tobigun/EavesDrum/doc/images/1.1/module.jpg

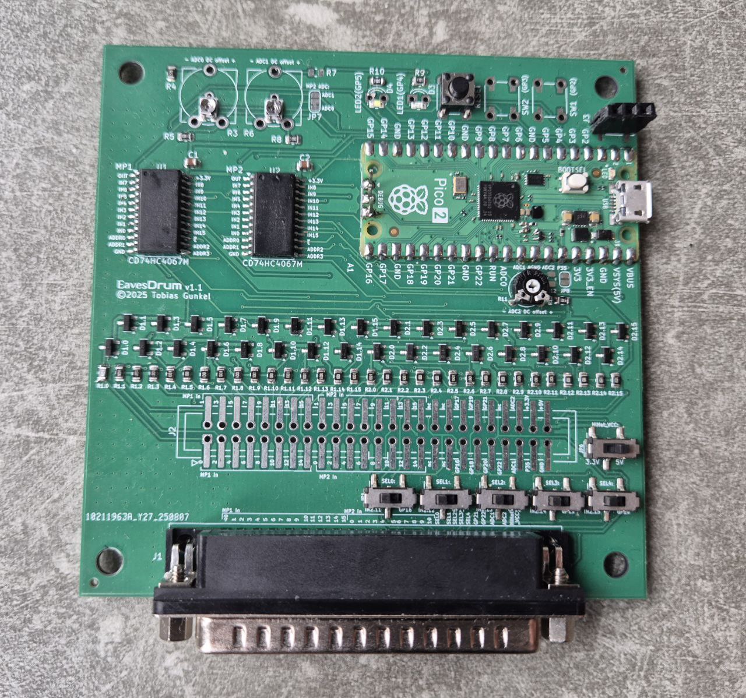
doc/images/1.1/module.jpg
