tobigun/EavesDrum/doc/images/1.2/subd44.png

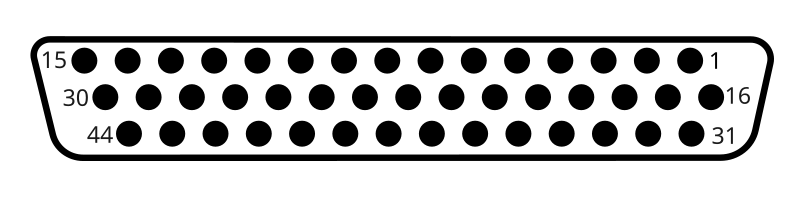
doc/images/1.2/subd44.png
