tobigun/EavesDrum/doc/latency/CMedia-Stick.png

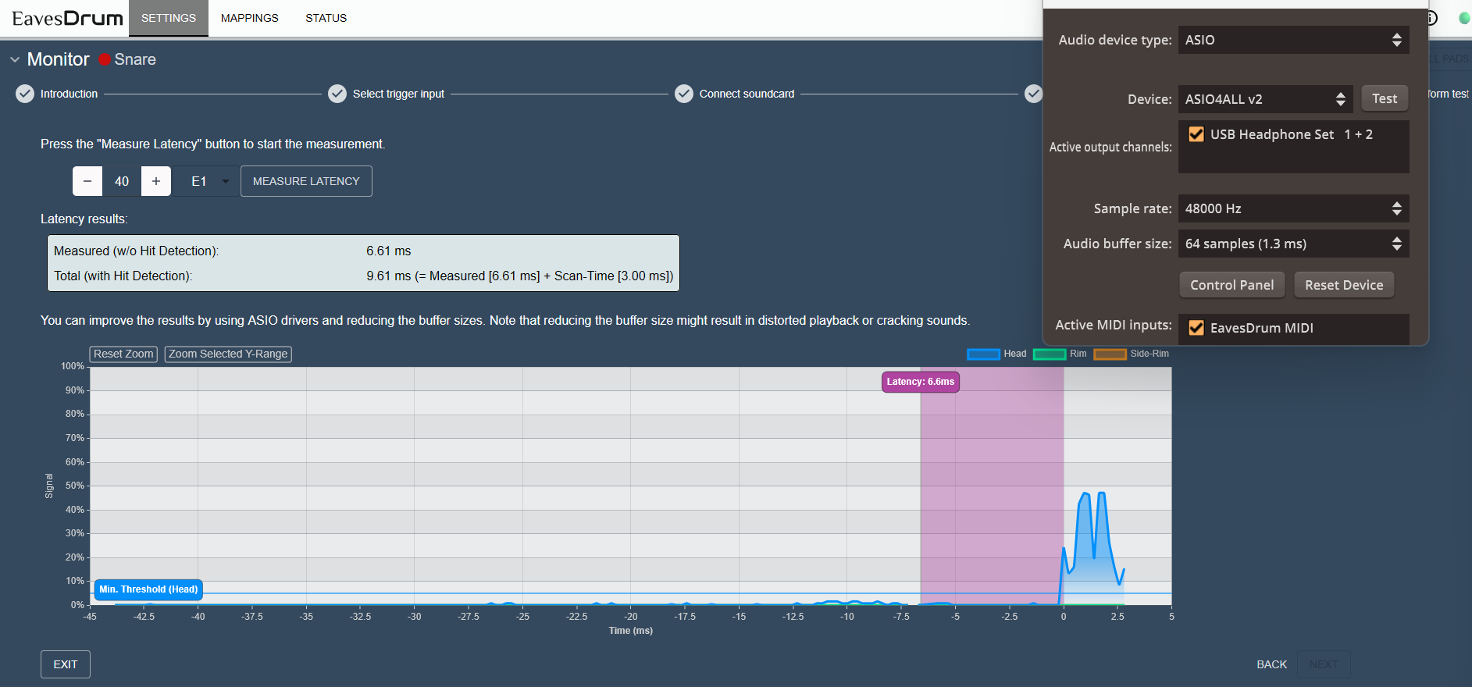
doc/latency/CMedia-Stick.png
