tobigun/EavesDrum/doc/latency/efnote3-asus.png

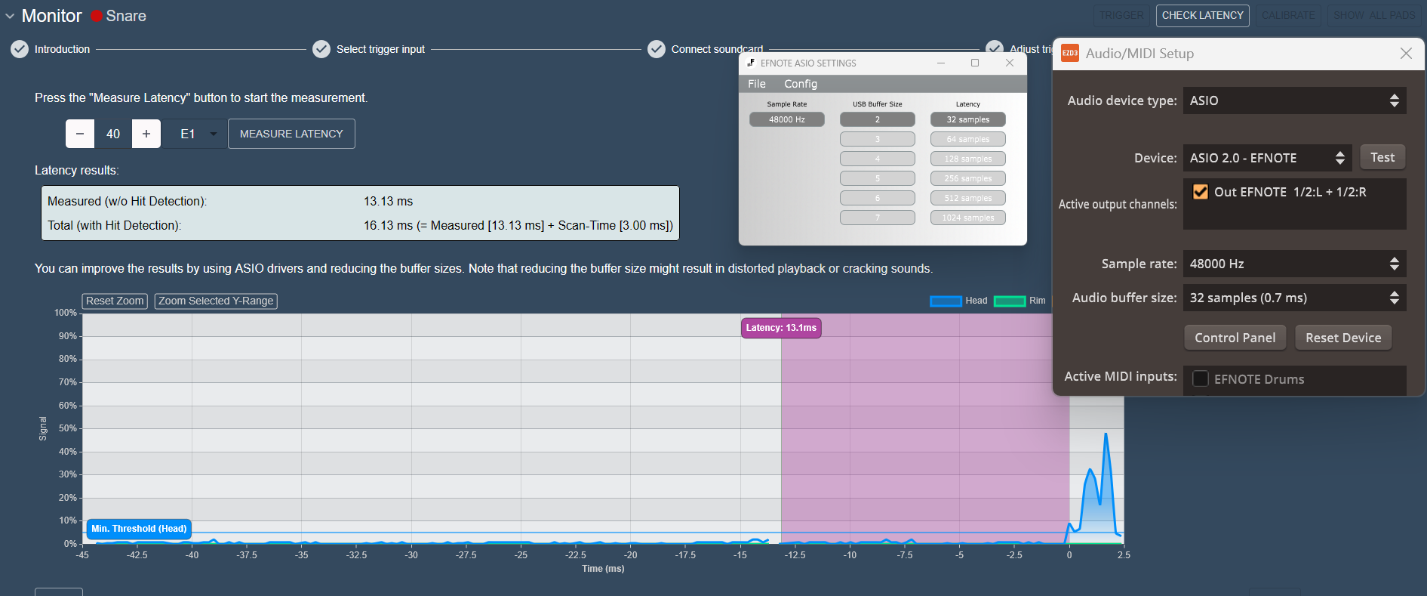
doc/latency/efnote3-asus.png
