tobigun/EavesDrum/doc/latency/efnote3-hp.png

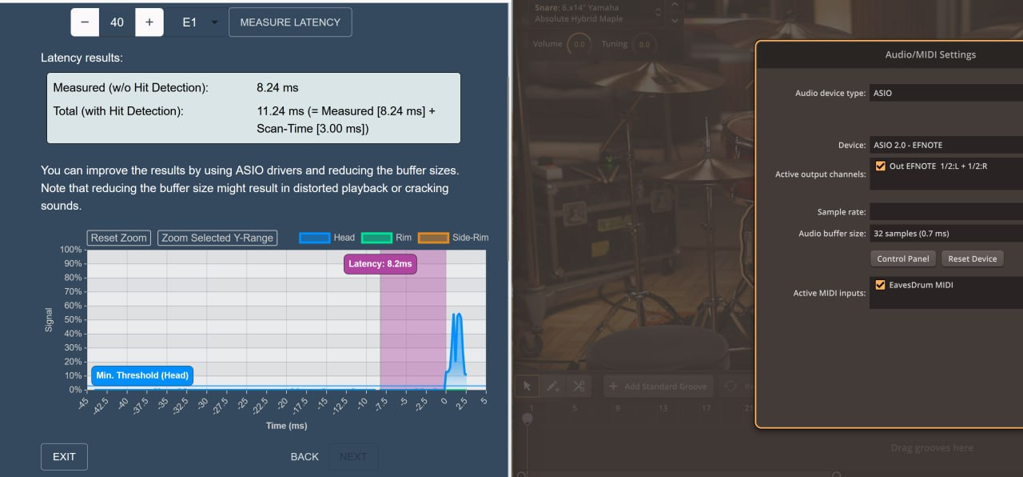
doc/latency/efnote3-hp.png
