tobigun/EavesDrum/doc/latency/focusrite-48kHz-hp.jpg

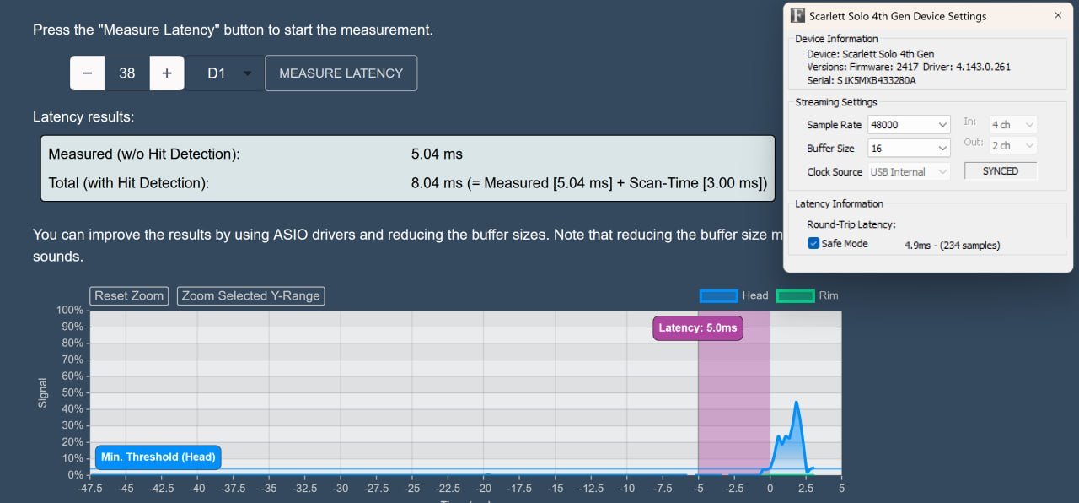
doc/latency/focusrite-48kHz-hp.jpg
