tobigun/EavesDrum/doc/latency/focusrite-192kHz-asus.png

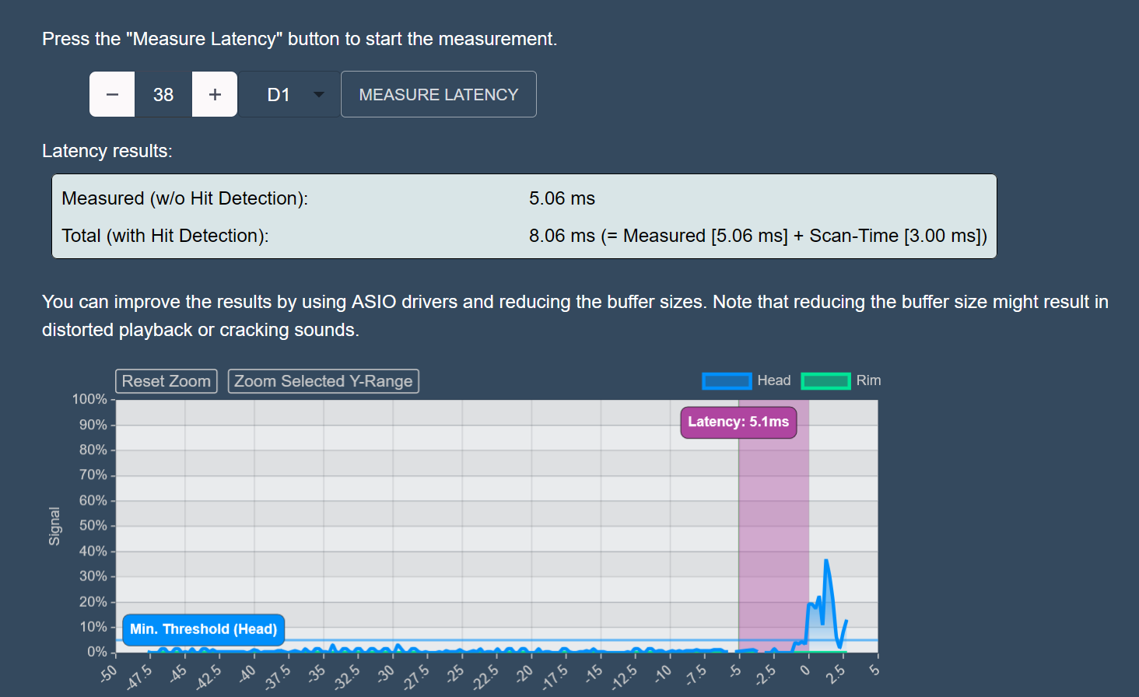
doc/latency/focusrite-192kHz-asus.png
