tobigun/EavesDrum/doc/latency/Headphone-Adapter-AB13X.png

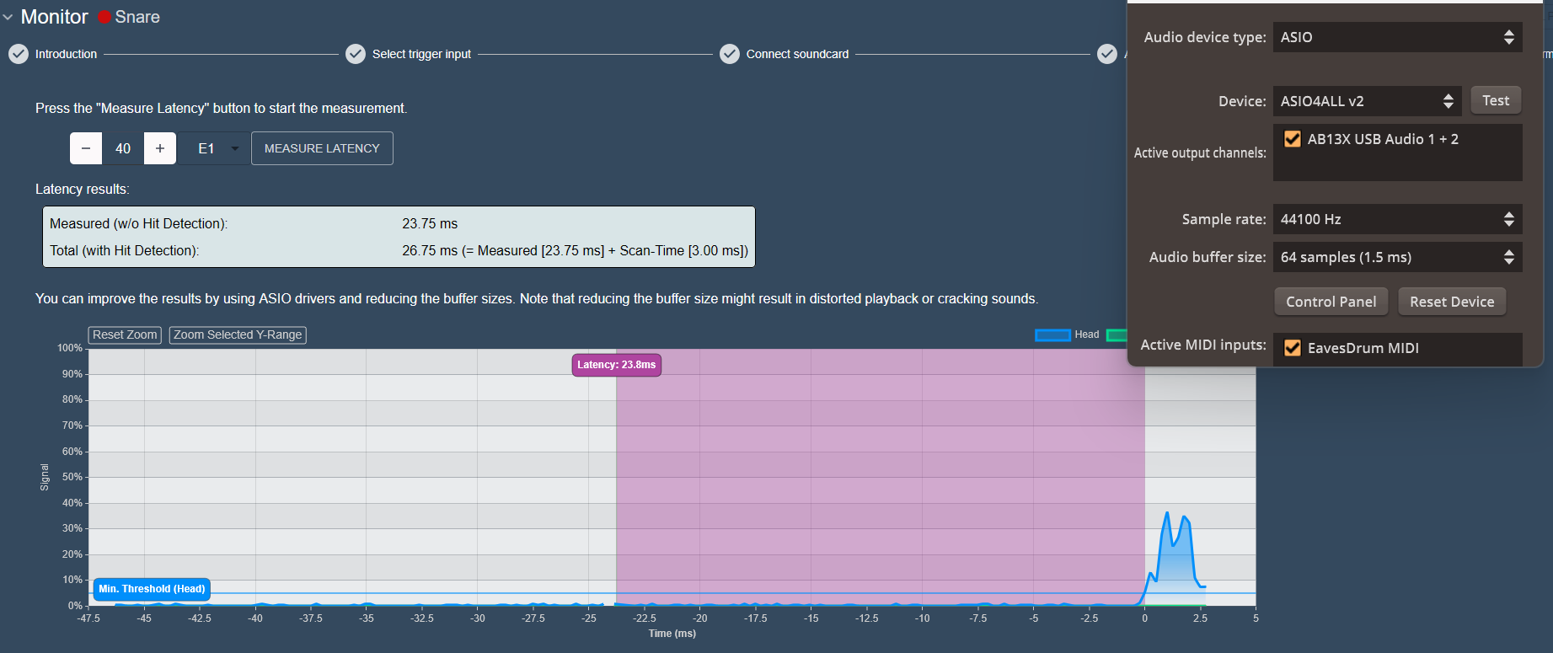
doc/latency/Headphone-Adapter-AB13X.png
