tobigun/EavesDrum/doc/latency/nux-mighty-plug-pro.png

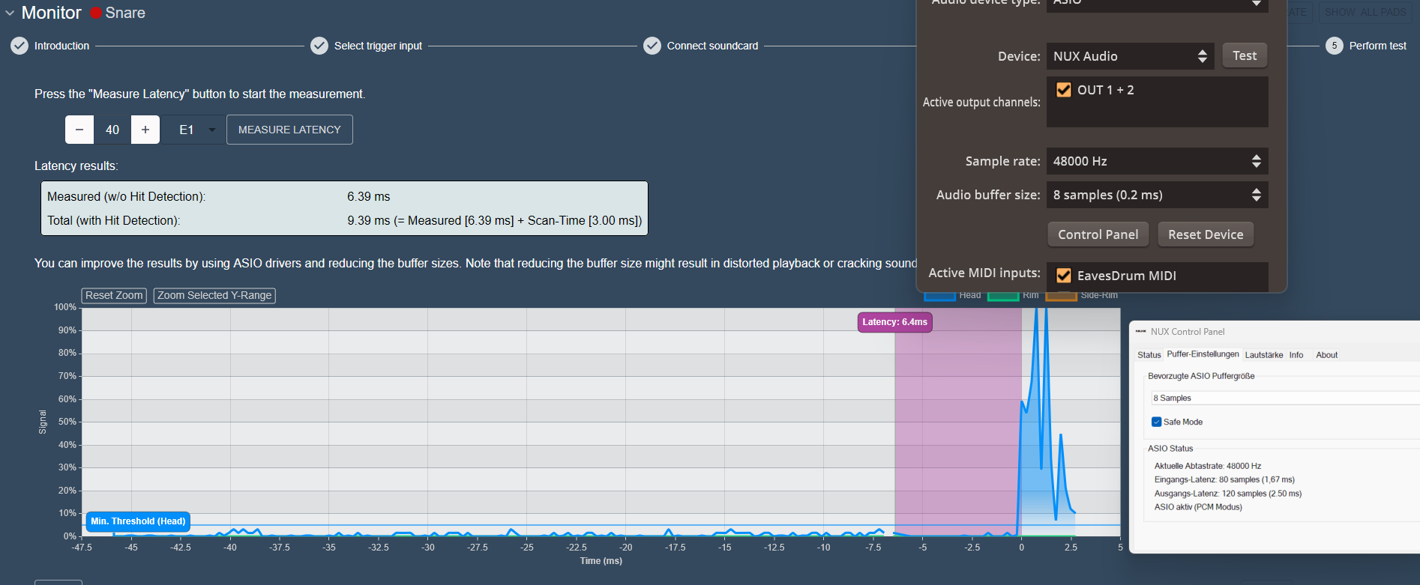
doc/latency/nux-mighty-plug-pro.png
