tobigun/EavesDrum/doc/latency/nux-mighty-plug.png

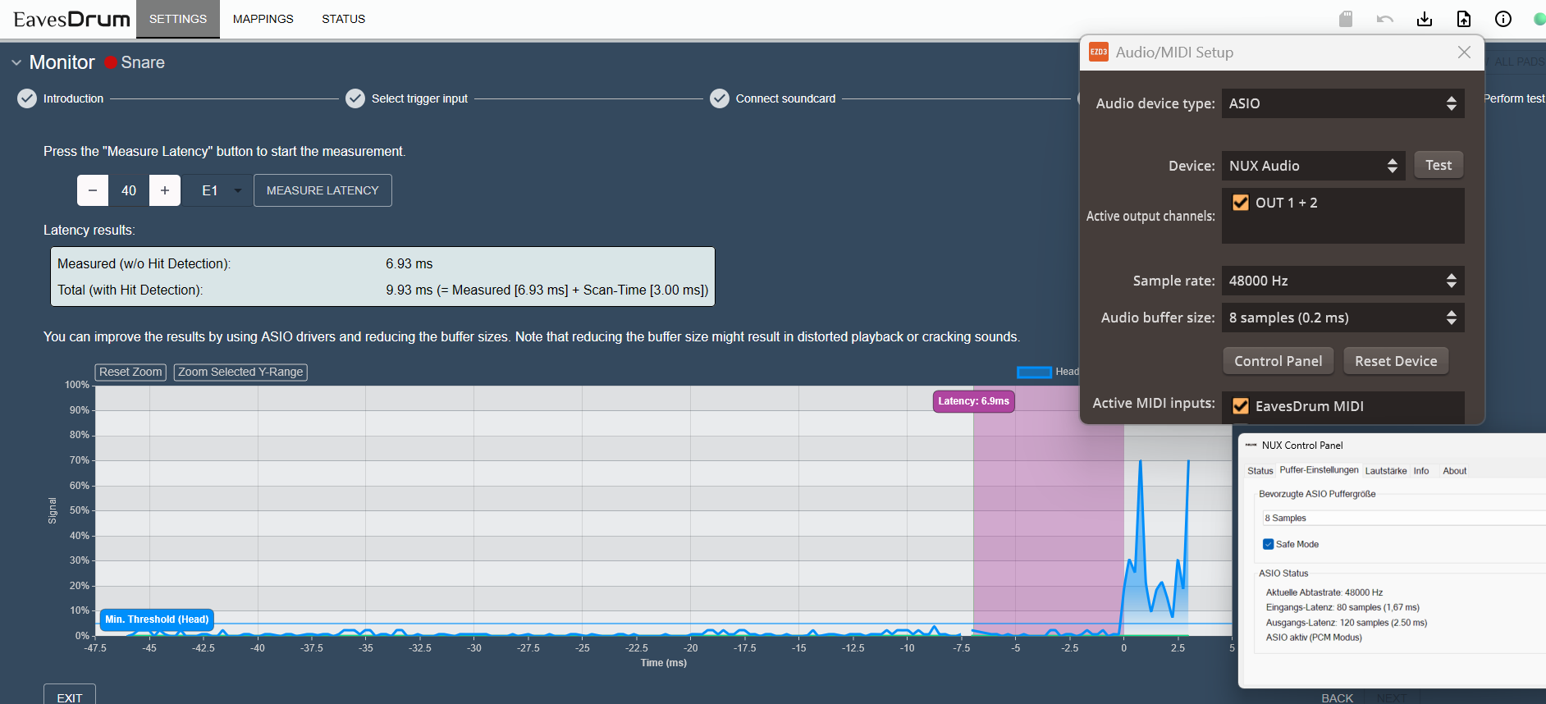
doc/latency/nux-mighty-plug.png
