tobigun/EavesDrum/doc/latency/realtek293-asio.jpg

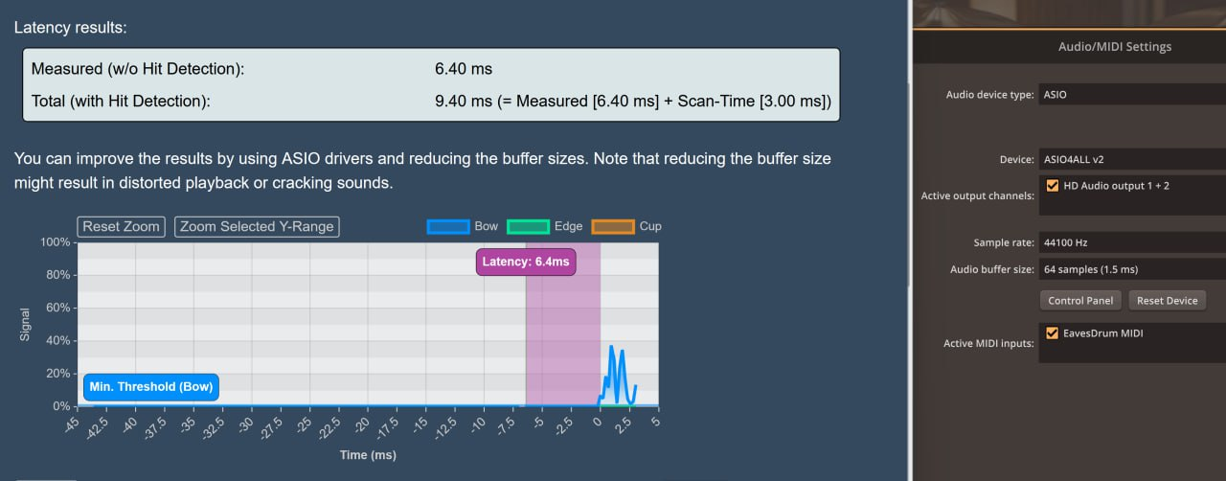
doc/latency/realtek293-asio.jpg
