tobigun/EavesDrum/doc/latency/realtek293-wasapi-exclusive.jpg

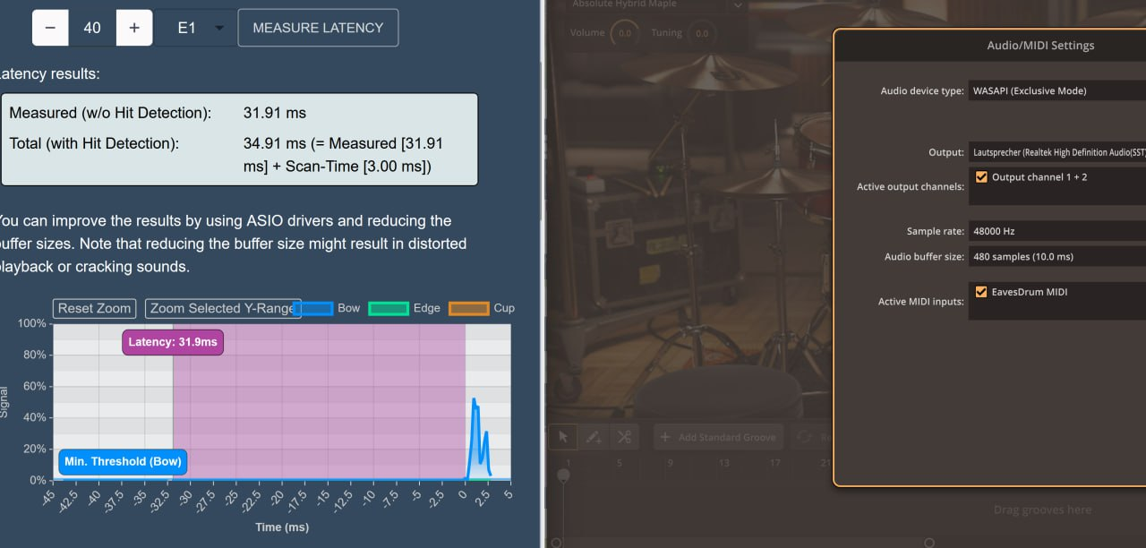
doc/latency/realtek293-wasapi-exclusive.jpg
