tobigun/EavesDrum/doc/latency/realtek-asio.png

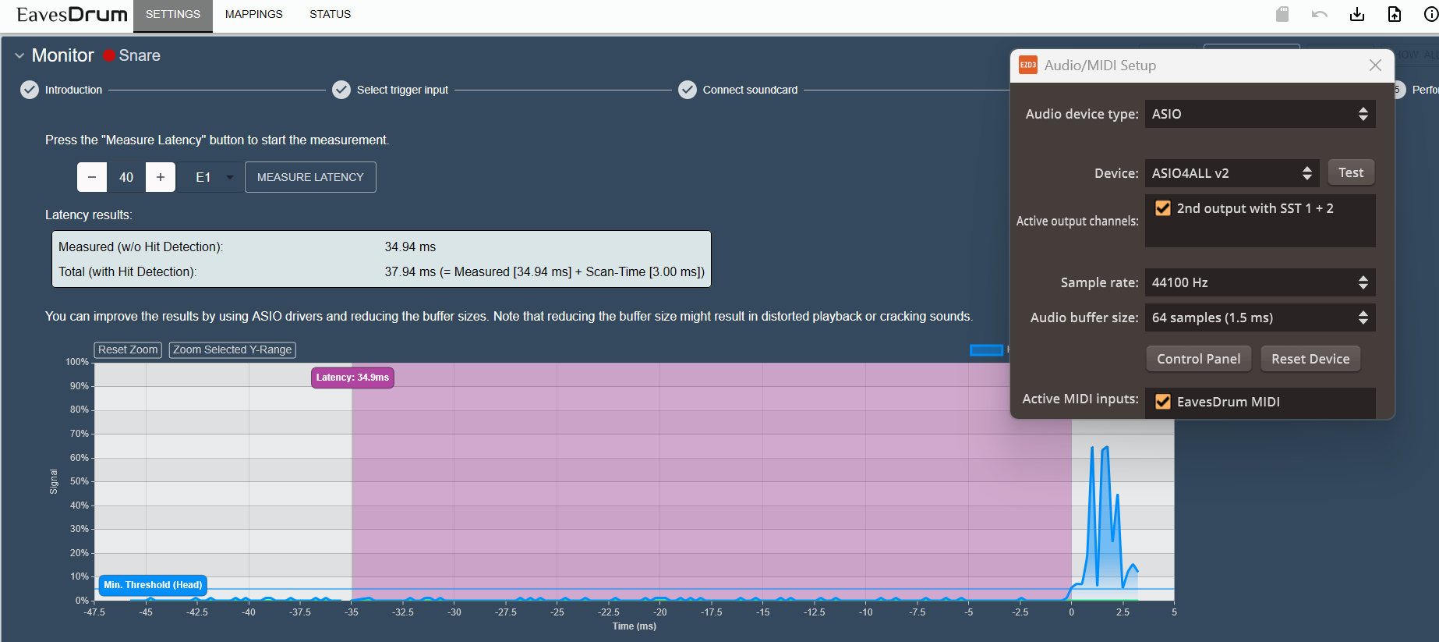
doc/latency/realtek-asio.png
