tobigun/EavesDrum/doc/latency/yamaha-ead10.jpg

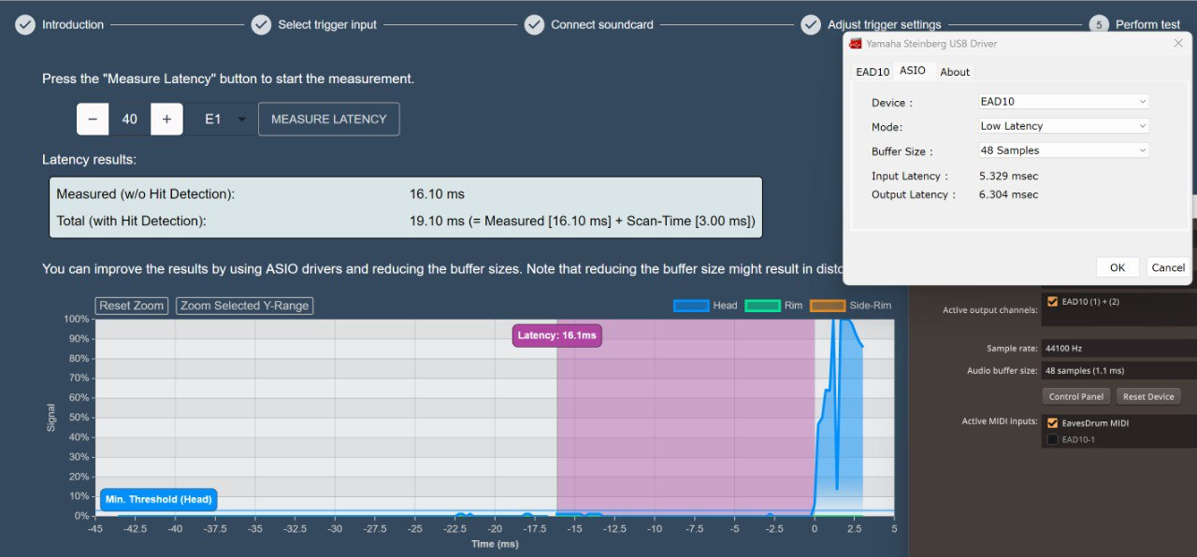
doc/latency/yamaha-ead10.jpg
