tobigun/EavesDrum/doc/simulation/drum-trigger.asc

D2: schottky; BAT54
D3: schottky; BAT54
R1: res; 2.7k
R2: res; 2.7k
R3: res; 1k
U1: MAX4051A
V1: voltage; 3.3
V2: voltage; SINE(0 10 50000); Cpar=20p
V3: voltage; SINE(0 3.3 0 0 0 0u 10u)
Named nets: 0
.tran 0.1m
