tobigun/EavesDrum/src/boards/rp2040/tusb_config.h

/*
 * The MIT License (MIT)
 *
 * Copyright (c) 2019 Ha Thach (tinyusb.org)
 *
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
 */

#ifndef _TUSB_CONFIG_H_
#define _TUSB_CONFIG_H_

#ifdef __cplusplus
extern "C" {
#endif

//--------------------------------------------------------------------+
// Board Specific Configuration
//--------------------------------------------------------------------+

// RHPort number used for device can be defined by board.mk, default to port 0
#ifndef BOARD_TUD_RHPORT
#define BOARD_TUD_RHPORT 0
#endif

// RHPort max operational speed can defined by board.mk
#ifndef BOARD_TUD_MAX_SPEED
#define BOARD_TUD_MAX_SPEED OPT_MODE_DEFAULT_SPEED
#endif

//--------------------------------------------------------------------
// Common Configuration
//--------------------------------------------------------------------

// defined by compiler flags for flexibility
#ifndef CFG_TUSB_MCU
#define CFG_TUSB_MCU OPT_MCU_RP2040
#endif

#define CFG_TUSB_RHPORT0_MODE OPT_MODE_DEVICE
#define CFG_TUSB_OS OPT_OS_PICO

// CFG_TUSB_DEBUG is defined by compiler in DEBUG build
#ifndef CFG_TUSB_DEBUG
#define CFG_TUSB_DEBUG 0
#endif

// Enable Device stack
#define CFG_TUD_ENABLED 1

// Default is max speed that hardware controller could support with on-chip PHY
// #define CFG_TUD_MAX_SPEED     BOARD_TUD_MAX_SPEED
#define CFG_TUD_NET_MTU 1500

/* USB DMA on some MCUs can only access a specific SRAM region with restriction on alignment.
 * Tinyusb use follows macros to declare transferring memory so that they can be put
 * into those specific section.
 * e.g
 * - CFG_TUSB_MEM SECTION : __attribute__ (( section(".usb_ram") ))
 * - CFG_TUSB_MEM_ALIGN   : __attribute__ ((aligned(4)))
 */
#ifndef CFG_TUSB_MEM_SECTION
#define CFG_TUSB_MEM_SECTION
#endif

#ifndef CFG_TUSB_MEM_ALIGN
#define CFG_TUSB_MEM_ALIGN __attribute__((aligned(4)))
#endif

//--------------------------------------------------------------------
// DEVICE CONFIGURATION
//--------------------------------------------------------------------

#ifndef CFG_TUD_ENDPOINT0_SIZE
#define CFG_TUD_ENDPOINT0_SIZE 64
#endif

//------------- CLASS -------------//
#define CFG_TUD_HID (1)

#ifndef ENABLE_USB_SERIAL
#define CFG_TUD_CDC (0)
#else
#define CFG_TUD_CDC (1)
#endif

#ifndef ENABLE_USB_MSC
#define CFG_TUD_MSC (0)
#else
#define CFG_TUD_MSC (1)
#endif

#ifdef DISABLE_USB_MIDI
#define CFG_TUD_MIDI (0)
#else
#define CFG_TUD_MIDI (1)
#endif

#define CFG_TUD_VENDOR (0)

// Network class has 2 drivers: ECM/RNDIS and NCM.
// Only one of the drivers can be enabled
#ifdef ENABLE_USB_NET_RNDIS
#define CFG_TUD_ECM_RNDIS (1)
#else
#define CFG_TUD_ECM_RNDIS (0)
#endif
#define CFG_TUD_NCM (1 - CFG_TUD_ECM_RNDIS)

#if CFG_TUD_CDC
#define CFG_TUD_CDC_RX_BUFSIZE (256)
#define CFG_TUD_CDC_TX_BUFSIZE (256)
#endif

#if CFG_TUD_MSC
#define CFG_TUD_MSC_EP_BUFSIZE (64)
#endif

#if CFG_TUD_HID
// HID buffer size Should be sufficient to hold ID (if any) + Data
#define CFG_TUD_HID_EP_BUFSIZE (64)
#endif

#if CFG_TUD_MIDI
// MIDI FIFO size of TX and RX
#define CFG_TUD_MIDI_RX_BUFSIZE 128
#define CFG_TUD_MIDI_TX_BUFSIZE 128
#endif

//--------------------------------------------------------------------
// HOST CONFIGURATION
//--------------------------------------------------------------------

/* USB DMA on some MCUs can only access a specific SRAM region with restriction on alignment.
 * Tinyusb use follows macros to declare transferring memory so that they can be put
 * into those specific section.
 * e.g
 * - CFG_TUSB_MEM SECTION : __attribute__ (( section(".usb_ram") ))
 * - CFG_TUSB_MEM_ALIGN   : __attribute__ ((aligned(4)))
 */
#ifndef CFG_TUH_MEM_SECTION
#define CFG_TUH_MEM_SECTION
#endif

#ifndef CFG_TUH_MEM_ALIGN
#define CFG_TUH_MEM_ALIGN     __attribute__ ((aligned(4)))
#endif

// Enable Host stack
#define CFG_TUH_ENABLED       1
#define CFG_TUH_RPI_PIO_USB   1

#if CFG_TUSB_MCU == OPT_MCU_RP2040
  // #define CFG_TUH_RPI_PIO_USB   1 // use pio-usb as host controller
  // host roothub port is 1 if using either pio-usb or max3421
  #if (defined(CFG_TUH_RPI_PIO_USB) && CFG_TUH_RPI_PIO_USB)
    #define BOARD_TUH_RHPORT      1
  #endif
#endif

#define CFG_TUH_MAX_SPEED     BOARD_TUH_MAX_SPEED

//------------------------- Board Specific --------------------------

// RHPort number used for host can be defined by board.mk, default to port 0
#ifndef BOARD_TUH_RHPORT
#define BOARD_TUH_RHPORT      0
#endif

// RHPort max operational speed can defined by board.mk
#ifndef BOARD_TUH_MAX_SPEED
#define BOARD_TUH_MAX_SPEED   OPT_MODE_DEFAULT_SPEED
#endif

//--------------------------------------------------------------------
// Driver Configuration
//--------------------------------------------------------------------

// Size of buffer to hold descriptors and other data used for enumeration
#define CFG_TUH_ENUMERATION_BUFSIZE 512

#define CFG_TUH_HUB                 1 // number of supported hubs
#define CFG_TUH_MIDI                1
#define CFG_TUH_HID                 1
#define CFG_TUH_CDC                 0
#define CFG_TUH_MSC                 0
#define CFG_TUH_VENDOR              0

// max device support (excluding hub device): 1 hub typically has 4 ports
#define CFG_TUH_DEVICE_MAX          (3*CFG_TUH_HUB + 1)


#ifdef __cplusplus
}
#endif

#endif /* _TUSB_CONFIG_H_ */
