tobigun/EavesDrum/src/boards/rp2040/network_usb.cpp

/*
 * The MIT License (MIT)
 *
 * Copyright (c) 2020 Peter Lawrence
 * Copyright (c) 2025 Tobias Gunkel
 *
 * influenced by lrndis https://github.com/fetisov/lrndis
 *
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
 * THE SOFTWARE IS PROVIDED "AS IS", WITHOUT WARRANTY OF ANY KIND, EXPRESS OR
 * IMPLIED, INCLUDING BUT NOT LIMITED TO THE WARRANTIES OF MERCHANTABILITY,
 * FITNESS FOR A PARTICULAR PURPOSE AND NONINFRINGEMENT. IN NO EVENT SHALL THE
 * AUTHORS OR COPYRIGHT HOLDERS BE LIABLE FOR ANY CLAIM, DAMAGES OR OTHER
 * LIABILITY, WHETHER IN AN ACTION OF CONTRACT, TORT OR OTHERWISE, ARISING FROM,
 * OUT OF OR IN CONNECTION WITH THE SOFTWARE OR THE USE OR OTHER DEALINGS IN
 * THE SOFTWARE.
 */

 #include "network_connection.h"

#include "drum_io.h"

#include <tusb.h>

extern "C"
{
#include "dhserver.h"
#include "dnserver.h"
}

#include "lwip/ethip6.h"
#include "lwip/init.h"
#include "lwip/netif.h"
#include "lwip/timeouts.h"

#define INIT_IP4(a, b, c, d) {PP_HTONL(LWIP_MAKEU32(a, b, c, d))}

#define DNS_DOMAIN_NAME "drum"
#define DNS_HOST_NAME "eaves"

// lwip context
static struct netif netif_data;

// shared between tud_network_recv_cb() and service_traffic()
static struct pbuf* received_frame = 0;

static bool usb_link_up = false;

static void apply_link_state(bool is_up) {
  usb_link_up = is_up;
  if (is_up) {
    netif_set_link_up(&netif_data);
  } else {
    netif_set_link_down(&netif_data);
  }

  // RP2040 device stack is always on rhport 0
  tud_network_link_state(0, is_up);
}

/*
 * this is used by this code, ./class/net/net_driver.c, and usb_descriptors.c
 * ideally speaking, this should be generated from the hardware's unique ID (if available)
 * it is suggested that the first byte is 0x02 to indicate a link-local address
 */
uint8_t tud_network_mac_address[6] = {0x02, 0x02, 0x84, 0x6A, 0x96, 0x00};

// network parameters of this MCU
static const ip4_addr_t ipaddr = INIT_IP4(192, 168, 7, 1);
static const ip4_addr_t netmask = INIT_IP4(255, 255, 255, 0);
static const ip4_addr_t gateway = INIT_IP4(0, 0, 0, 0);

// database IP addresses that can be offered to the host; this must be in RAM to store assigned MAC addresses
static dhcp_entry_t entries[] = {
    // mac ip address lease time
    {{0}, INIT_IP4(192, 168, 7, 2), 24 * 60 * 60},
    {{0}, INIT_IP4(192, 168, 7, 3), 24 * 60 * 60},
    {{0}, INIT_IP4(192, 168, 7, 4), 24 * 60 * 60},
};

static const dhcp_config_t dhcp_config = {
    .router = INIT_IP4(0, 0, 0, 0), // router address (if any)
    .port = 67, // listen port
    .dns = INIT_IP4(192, 168, 7, 1), // dns server (if any)
    .domain = DNS_DOMAIN_NAME,
    .num_entry = TU_ARRAY_SIZE(entries),
    .entries = entries};

static err_t linkoutput_fn(struct netif* netif, struct pbuf* p) {
  (void)netif;

  while (true) {
    // if TinyUSB isn't ready, we must signal back to lwip that there is nothing we can do
    if (!tud_ready())
      return ERR_USE;

    // if the network driver can accept another packet, we make it happen
    if (tud_network_can_xmit(p->tot_len)) {
      DrumIO::led(LedId::Network, false);
      tud_network_xmit(p, 0 /* unused for this example */);
      return ERR_OK;
    }

    // transfer execution to TinyUSB in the hopes that it will finish transmitting the prior packet
    tud_task();
  }
}

static err_t ip4_output_fn(struct netif* netif, struct pbuf* p, const ip4_addr_t* addr) {
  return etharp_output(netif, p, addr);
}

#if LWIP_IPV6
static err_t ip6_output_fn(struct netif* netif, struct pbuf* p, const ip6_addr_t* addr) {
  return ethip6_output(netif, p, addr);
}
#endif

static err_t netif_init_cb(struct netif* netif) {
  LWIP_ASSERT("netif != NULL", (netif != NULL));
  netif->mtu = CFG_TUD_NET_MTU;
  netif->flags = NETIF_FLAG_BROADCAST | NETIF_FLAG_ETHARP | NETIF_FLAG_LINK_UP | NETIF_FLAG_UP;
  netif->state = NULL;
  netif->name[0] = 'E';
  netif->name[1] = 'X';
  netif->linkoutput = linkoutput_fn;
  netif->output = ip4_output_fn;
#if LWIP_IPV6
  netif->output_ip6 = ip6_output_fn;
#endif
  return ERR_OK;
}

static void init_lwip() {
  struct netif* netif = &netif_data;

  lwip_init();

  // the lwip virtual MAC address must be different from the host's; to ensure this, we toggle the LSbit
  netif->hwaddr_len = sizeof(tud_network_mac_address);
  memcpy(netif->hwaddr, tud_network_mac_address, sizeof(tud_network_mac_address));
  netif->hwaddr[5] ^= 0x01;

  netif = netif_add(netif, &ipaddr, &netmask, &gateway, NULL, netif_init_cb, ip_input);
#if LWIP_IPV6
  netif_create_ip6_linklocal_address(netif, 1);
#endif
  netif_set_default(netif);
  apply_link_state(false);
}

extern "C" void tud_mount_cb(void) {
  apply_link_state(true);
}

extern "C" void tud_umount_cb(void) {
  apply_link_state(false);
}

extern "C" void tud_suspend_cb(bool /*remote_wakeup_en*/) {
  apply_link_state(false);
}

extern "C" void tud_resume_cb(void) {
  apply_link_state(true);
}

/* handle any DNS requests from dns-server */
bool dns_query_proc(const char* name, ip4_addr_t* addr) {
  if (0 == strcmp(name, DNS_HOST_NAME "." DNS_DOMAIN_NAME)) {
    *addr = ipaddr;
    return true;
  }
  return false;
}

bool tud_network_recv_cb(const uint8_t* src, uint16_t size) {
  // this shouldn't happen, but if we get another packet before parsing the previous, we must signal our inability to accept it
  if (received_frame)
    return false;

  if (size) {
    struct pbuf* frame_buffer = pbuf_alloc(PBUF_RAW, size, PBUF_POOL);
    if (frame_buffer) {
      // pbuf_alloc() has already initialized struct; all we need to do is copy the data
      memcpy(frame_buffer->payload, src, size);

      // store away the pointer for service_traffic() to later handle
      received_frame = frame_buffer;
    }
  }

  return true;
}

uint16_t tud_network_xmit_cb(uint8_t* dst, void* ref, uint16_t arg) {
  (void)arg; // unused for this example
  struct pbuf* p = (struct pbuf*)ref;

  return pbuf_copy_partial(p, dst, p->tot_len, 0);
}

void tud_network_init_cb() {
  // if the network is re-initializing and we have a leftover packet, we must do a cleanup
  if (received_frame) {
    pbuf_free(received_frame);
    received_frame = NULL;
  }
}

void NetworkUsb::update() {
  DrumIO::led(LedId::Network, true);
  // handle any packet received by tud_network_recv_cb()
  if (received_frame) {
    DrumIO::led(LedId::Network, false);
    ethernet_input(received_frame, &netif_data);
    // pbuf_free(received_frame);
    received_frame = NULL;
    tud_network_recv_renew();
  }

  sys_check_timeouts();
}

void NetworkUsb::begin() {
  init_lwip();
  while (!netif_is_up(&netif_data)) {}

  DrumIO::led(LedId::Network, true); // indicate that the network is up

  while (dhserv_init(&dhcp_config) != ERR_OK) {}
  while (dnserv_init(IP_ADDR_ANY, 53, dns_query_proc) != ERR_OK) {}
}
