tobigun/EavesDrum/src/drum/drum.h

// Copyright (c) 2025 Tobias Gunkel
// SPDX-License-Identifier: GPL-3.0-or-later

#pragma once

#include "types.h"
#include "log.h"
#include "drum_io.h"
#include "drum_mappings.h"
#include "drum_mux.h"
#include "drum_pad.h"
#include "drum_connector.h"
#include "drum_settings.h"
