tobigun/EavesDrum/src/boards/rp2040/SerialUSB.cpp

/*
    Serial-Over-USB for the Raspberry Pi Pico RP2040
    Implements an ACM which will reboot into UF2 mode on a 1200bps DTR toggle.
    Much of this was modified from the Raspberry Pi Pico SDK stdio_usb.c file.

    Copyright (c) 2021 Earle F. Philhower, III <earlephilhower@yahoo.com>

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
    You should have received a copy of the GNU Lesser General Public
    License along with this library; if not, write to the Free Software
    Foundation, Inc., 51 Franklin St, Fifth Floor, Boston, MA  02110-1301  USA
*/

#include <Arduino.h>
#include "CoreMutex.h"

#include <tusb.h>
#include <pico/time.h>
#include <pico/binary_info.h>
#include <pico/bootrom.h>
#include <hardware/irq.h>
#include <pico/mutex.h>
#include <hardware/watchdog.h>
#include <pico/unique_id.h>
#include <hardware/resets.h>

#if CFG_TUD_CDC
// Ensure we are installed in the USB chain
void __USBInstallSerial() { /* noop */ }

// SerialEvent functions are weak, so when the user doesn't define them,
// the linker just sets their address to 0 (which is checked below).
// The Serialx_available is just a wrapper around Serialx.available(),
// but we can refer to it weakly so we don't pull in the entire
// HardwareSerial instance if the user doesn't also refer to it.
extern void serialEvent() __attribute__((weak));


extern mutex_t __usb_mutex;

void SerialUSB::begin(unsigned long baud) {
    (void) baud; //ignored

    if (_running) {
        return;
    }

    _running = true;
}

void SerialUSB::end() {
    // TODO
}

int SerialUSB::peek() {
    CoreMutex m(&__usb_mutex, false);
    if (!_running || !m) {
        return 0;
    }

    uint8_t c;
    tud_task();
    return tud_cdc_peek(&c) ? (int) c : -1;
}

int SerialUSB::read() {
    CoreMutex m(&__usb_mutex, false);
    if (!_running || !m) {
        return -1;
    }

    tud_task();
    if (tud_cdc_available()) {
        return tud_cdc_read_char();
    }
    return -1;
}

int SerialUSB::available() {
    CoreMutex m(&__usb_mutex, false);
    if (!_running || !m) {
        return 0;
    }

    tud_task();
    return tud_cdc_available();
}

int SerialUSB::availableForWrite() {
    CoreMutex m(&__usb_mutex, false);
    if (!_running || !m) {
        return 0;
    }

    tud_task();
    return tud_cdc_write_available();
}

void SerialUSB::flush() {
    CoreMutex m(&__usb_mutex, false);
    if (!_running || !m) {
        return;
    }

    tud_cdc_write_flush();
    tud_task();
}

size_t SerialUSB::write(uint8_t c) {
    return write(&c, 1);
}

size_t SerialUSB::write(const uint8_t *buf, size_t length) {
    CoreMutex m(&__usb_mutex, false);
    if (!_running || !m) {
        return 0;
    }

    static uint64_t last_avail_time;
    int written = 0;
    if (tud_cdc_connected() || _ignoreFlowControl) {
        for (size_t i = 0; i < length;) {
            int n = length - i;
            int avail = tud_cdc_write_available();
            if (n > avail) {
                n = avail;
            }
            if (n) {
                int n2 = tud_cdc_write(buf + i, n);
                tud_task();
                tud_cdc_write_flush();
                i += n2;
                written += n2;
                last_avail_time = time_us_64();
            } else {
                tud_task();
                tud_cdc_write_flush();
                if (!tud_cdc_connected() ||
                        (!tud_cdc_write_available() && time_us_64() > last_avail_time + 1'000'000 /* 1 second */)) {
                    break;
                }
            }
        }
    } else {
        // reset our timeout
        last_avail_time = 0;
    }
    tud_task();
    return written;
}

SerialUSB::operator bool() {
    CoreMutex m(&__usb_mutex, false);
    if (!_running || !m) {
        return false;
    }

    tud_task();
    return tud_cdc_connected();
}

void SerialUSB::ignoreFlowControl(bool ignore) {
    _ignoreFlowControl = ignore;
}

static bool _dtr = false;
static bool _rts = false;
static int _bps = 115200;
static bool _rebooting = false;
static void CheckSerialReset() {
    if (!_rebooting && (_bps == 1200) && (!_dtr)) {
        if (__isFreeRTOS) {
            __freertos_idle_other_core();
        }
        _rebooting = true;
        // Disable NVIC IRQ, so that we don't get bothered anymore
        irq_set_enabled(USBCTRL_IRQ, false);
        // Reset the whole USB hardware block
        reset_block(RESETS_RESET_USBCTRL_BITS);
        unreset_block(RESETS_RESET_USBCTRL_BITS);
        // Delay a bit, so the PC can figure out that we have disconnected.
        busy_wait_ms(3);
        reset_usb_boot(0, 0);
        while (1); // WDT will fire here
    }
}

bool SerialUSB::dtr() {
    return _dtr;
}

bool SerialUSB::rts() {
    return _rts;
}

extern "C" void tud_cdc_line_state_cb(uint8_t itf, bool dtr, bool rts) {
    (void) itf;
    _dtr = dtr ? true : false;
    _rts = rts ? true : false;
    CheckSerialReset();
}

extern "C" void tud_cdc_line_coding_cb(uint8_t itf, cdc_line_coding_t const* p_line_coding) {
    (void) itf;
    _bps = p_line_coding->bit_rate;
    CheckSerialReset();
}

void arduino::serialEventRun(void) {
    if (serialEvent && Serial.available()) {
        serialEvent();
    }
}

#else

SerialUSB::SerialUSB() {}

void SerialUSB::begin(unsigned long baud) {
    _running = false;
}

void SerialUSB::end() {
}

int SerialUSB::peek() {
    return 0;
}

int SerialUSB::read() {
    return -1;
}

int SerialUSB::available() {
    return 0;
}

int SerialUSB::availableForWrite() {
    return 0;
}

void SerialUSB::flush() {
}

size_t SerialUSB::write(uint8_t c) {
    return write(&c, 1);
}

size_t SerialUSB::write(const uint8_t *buf, size_t length) {
    return 0;
}

SerialUSB::operator bool() {
    return false;
}

void SerialUSB::ignoreFlowControl(bool ignore) {
}

bool SerialUSB::dtr() {
    return false;
}

bool SerialUSB::rts() {
    return false;
}

#endif

SerialUSB Serial;
