tobigun/EavesDrum/src/boards/rp2040/SerialTxUART.h

/*
    Serial-over-UART for the Raspberry Pi Pico RP2040

    Copyright (c) 2021 Earle F. Philhower, III <earlephilhower@yahoo.com>

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
    You should have received a copy of the GNU Lesser General Public
    License along with this library; if not, write to the Free Software
    Foundation, Inc., 51 Franklin St, Fifth Floor, Boston, MA  02110-1301  USA
*/

#pragma once

#include <Arduino.h>
#include "api/HardwareSerial.h"
#include "CoreMutex.h"
#include "LocklessQueue.h"

extern "C" typedef struct uart_inst uart_inst_t;

// Copy of SerialUART that supports deactivation of the RX pin (which is not used when only sending MIDI) to save one pin.
#define UART_PIN_NOT_DEFINED      (255u)
class SerialTxUART : public arduino::HardwareSerial {
public:
    SerialTxUART(uart_inst_t *uart, pin_size_t tx, pin_size_t rx = UART_PIN_NOT_DEFINED, pin_size_t rts = UART_PIN_NOT_DEFINED, pin_size_t cts = UART_PIN_NOT_DEFINED);

    // Select the pinout.  Call before .begin()
    bool setRX(pin_size_t pin);
    bool setTX(pin_size_t pin);
    bool setRTS(pin_size_t pin);
    bool setCTS(pin_size_t pin);
    bool setPinout(pin_size_t tx, pin_size_t rx) {
        bool ret = setRX(rx);
        ret &= setTX(tx);
        return ret;
    }

    bool setInvertTX(bool invert = true) {
        if (!_running) {
            _invertTX = invert;
        }
        return !_running;
    }
    bool setInvertRX(bool invert = true) {
        if (!_running) {
            _invertRX = invert;
        }
        return !_running;
    }
    bool setInvertControl(bool invert = true) {
        if (!_running) {
            _invertControl = invert;
        }
        return !_running;
    }

    bool setFIFOSize(size_t size);
    bool setPollingMode(bool mode = true);

    void begin(unsigned long baud = 115200) override {
        begin(baud, SERIAL_8N1);
    };
    void begin(unsigned long baud, uint16_t config) override;
    void end() override;

    virtual int peek() override;
    virtual int read() override;
    virtual int available() override;
    virtual int availableForWrite() override;
    virtual void flush() override;
    virtual size_t write(uint8_t c) override;
    virtual size_t write(const uint8_t *p, size_t len) override;
    using Print::write;
    bool overflow();
    operator bool() override;

    // ESP8266 compat
    void setDebugOutput(bool unused) {
        (void) unused;
    }

    // Allows the user to sleep until a break is received (self-clears the flag
    // on read)
    bool getBreakReceived();

    // Returns the baud rate the uart is actually operating at vs the desired baud rate specified to begin()
    int getActualBaud() {
        return _running ? _actualBaud : 0;
    }

private:
    static void _uart0IRQ();
    static void _uart1IRQ();
    void _handleIRQ(bool inIRQ = true);

    bool _running = false;
    uart_inst_t *_uart;
    pin_size_t _tx, _rx;
    pin_size_t _rts, _cts;
    gpio_function_t _fcnTx, _fcnRx, _fcnRts, _fcnCts;
    int _baud;
    int _actualBaud;
    mutex_t _mutex;
    bool _polling = false;
    bool _overflow;
    bool _break;
    bool _invertTX, _invertRX, _invertControl;

    LocklessQueue<uint8_t> *_queue;
    size_t   _fifoSize = 32;
    mutex_t  _fifoMutex; // Only needed when non-IRQ updates _writer
    void _pumpFIFO(); // User space FIFO transfer
};

extern SerialTxUART SerialTx1; // HW UART 0
extern SerialTxUART SerialTx2; // HW UART 1

namespace arduino {
extern void serialEvent1Run(void) __attribute__((weak));
extern void serialEvent2Run(void) __attribute__((weak));
};
