tobigun/EavesDrum/src/boards/native/AsyncWebServer/ESPAsyncWebServer.h

/*
  Asynchronous WebServer library for Espressif MCUs

  Copyright (c) 2016 Hristo Gochkov. All rights reserved.
  Copyright (c) 2025 Tobias Gunkel. All rights reserved.
  This file is part of the esp8266 core for Arduino environment.

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
  You should have received a copy of the GNU Lesser General Public
  License along with this library; if not, write to the Free Software
  Foundation, Inc., 51 Franklin St, Fifth Floor, Boston, MA  02110-1301  USA
*/

#pragma once

#include <Arduino.h>
#include <FS.h>
#include <functional>
#include <map>

class AsyncWebSocket;
class AsyncWebSocketClient;
class AsyncWebServer;
using AsyncStaticWebHandler = AsyncWebServer;

typedef enum {
  WS_EVT_CONNECT,
  WS_EVT_DISCONNECT,
  WS_EVT_PONG,
  WS_EVT_ERROR,
  WS_EVT_DATA
} AwsEventType;

typedef std::function<
    void(AsyncWebSocket* server, AsyncWebSocketClient* client, AwsEventType type, void* arg, uint8_t* data, size_t len)>
    AwsEventHandler;

class AsyncWebServerRequest {
public:
  void send(int code, const char* content_type = "text/html", const String& content = "") {
    this->content = content;
  }

  String content;
};

using ArRequestHandlerFunction = std::function<void(AsyncWebServerRequest* request)>;

class AsyncWebServer {
public:
  AsyncWebServer(int port)
    : _port(port) {}

  void begin();

  static void poll();

  void addHandler(AsyncWebSocket* webSocketServer);

  AsyncStaticWebHandler& serveStatic(const char* uri, fs::FS& fs, const char* path, const char* cache_control = nullptr) {
    // dummy
    return *this;
  }

  AsyncStaticWebHandler& setDefaultFile(const char* filename) {
    _defaultFilename = filename;
    return *this;
  }

  void onNotFound(ArRequestHandlerFunction onRequest) {
    AsyncWebServerRequest notFoundRequest;
    onRequest(&notFoundRequest);
    _notFoundContent = notFoundRequest.content;
  }

private:
  int _port;
  const char* _defaultFilename;

public:
  AsyncWebSocket* _webSocketServer;
  String _notFoundContent;
};

class AsyncWebSocketClient {
public:
  AsyncWebSocketClient(void* connection)
    : _connection(connection) {}

  uint32_t id() const;
  void text(const String& t);
  bool canSend() { return true; }
  void setCloseClientOnQueueFull(bool close) {}
  void ping() {}

  void binary(uint8_t* message, size_t len);

private:
  void* _connection;
};

typedef enum
{
  WS_CONTINUATION,
  WS_TEXT,
  WS_BINARY,
  WS_DISCONNECT = 0x08,
  WS_PING,
  WS_PONG
} AwsFrameType;

struct AwsFrameInfo {
  bool final;
  uint8_t message_opcode;
  size_t len;
  size_t index;
  uint8_t num;
};

class AsyncWebSocket {
public:
  AsyncWebSocket(const char* root)
    : _root(root) {}

  void addHandler(AsyncWebServer* webServer) {
    _webServer = webServer;
  }

  size_t count() {
    return _connections.size();
  }

  bool hasClient(int id) {
    return _connections.find(id) != _connections.end();
  }

  AsyncWebSocketClient*& client(int id) {
    return _connections[id];
  }

  void onEvent(AwsEventHandler handler) {
    _handler = handler;
  }
  
  void removeClient(int id) {
    _connections.erase(id);
  }

  void textAll(const String& message) {
    for (auto& [id, client] : _connections) {
      client->text(message);
    }
  }
  
  void binaryAll(uint8_t* message, size_t len) {
    for (auto& [id, client] : _connections) {
      client->binary(message, len);
    }
  }

private:
  const char* _root;
  std::map<int, AsyncWebSocketClient*> _connections;

public:
  AwsEventHandler _handler;
  AsyncWebServer* _webServer;
};
