tobigun/EavesDrum/src/boards/esp32/midi_transport_esp32_ble_midi.h

// Copyright (c) 2025 Tobias Gunkel
// SPDX-License-Identifier: GPL-3.0-or-later

#pragma once

#include "midi_transport.h"

#include <BLEMidi.h>

class MidiTransport_Esp32BleMidi : public MidiTransport {
public:
  virtual void start(MidiOutputMode mode) override;
  virtual void sendNoteOn(uint8_t inNoteNumber, uint8_t inVelocity, midi_channel_t inChannel) override;
  virtual void sendNoteOff(uint8_t inNoteNumber, uint8_t inVelocity, midi_channel_t inChannel) override;
  virtual void sendAfterTouch(uint8_t inPressure, midi_channel_t inChannel) override;
  virtual void sendAfterTouch(uint8_t inNoteNumber, uint8_t inPressure, midi_channel_t inChannel) override;
  virtual void sendControlChange(uint8_t inControlNumber, uint8_t inControlValue, midi_channel_t inChannel) override;
};
