tobigun/EavesDrum/src/log.cpp

// Copyright (c) 2026 Tobias Gunkel
// SPDX-License-Identifier: GPL-3.0-or-later

#include "log.h"

#include "event_log.h"

static Level minLogLevel = DEFAULT_LOG_LEVEL;

const char* levelToString(Level level) {
  switch (level) {
  case Level::Debug:
    return "DEBUG: ";
  case Level::Info:
    return "INFO: ";
  case Level::Error:
    return "ERROR: ";
  case Level::Warn:
    return "WARN: ";
  default:
    return "";
  }
}

void setLogLevel(Level level) {
  minLogLevel = level;
}

#ifdef ENABLE_SERIAL_DEBUG
static void logCharBuffer(Level level, const char* message, LogMode mode) {
  SerialDebug.printf("%s%s%s",
    mode == LogMode::NoPrefixOrNewline ? "" : levelToString(level),
    message,
    mode == LogMode::Default ? "\n" : "");
}
#endif

void logString(Level level, String message, LogMode mode) {
#ifdef ENABLE_SERIAL_DEBUG
  if (minLogLevel != Level::None && level >= minLogLevel) {
    logCharBuffer(level, message.c_str(), mode);
  }
#endif
}

#ifdef ENABLE_SERIAL_DEBUG
#define LOG_PRINTF(level, mode) \
  if (level < minLogLevel) return; \
  va_list args; \
  va_start(args, format); \
  char formatBuffer[256]; \
  vsnprintf(formatBuffer, sizeof(formatBuffer), format, args); \
  logCharBuffer(level, formatBuffer, mode); \
  va_end(args);
#else
#define LOG_PRINTF(level, mode) do {} while(0)
#endif

void logDebug(const char* format, ...) {
  LOG_PRINTF(Level::Debug, LogMode::Default);
}

void logInfo(const char* format, ...) {
  LOG_PRINTF(Level::Info, LogMode::Default);
}

void logWarn(const char* format, ...) {
  LOG_PRINTF(Level::Warn, LogMode::Default);
}

void logError(const char* format, ...) {
  LOG_PRINTF(Level::Error, LogMode::Default);
}

void logRaw(const char* format, ...) {
  LOG_PRINTF(Level::Info, LogMode::NoPrefixOrNewline);
}
